dcdlsd/Atari-NetworkBox/images/prototype/networkbox-on-atari-st-front.jpg

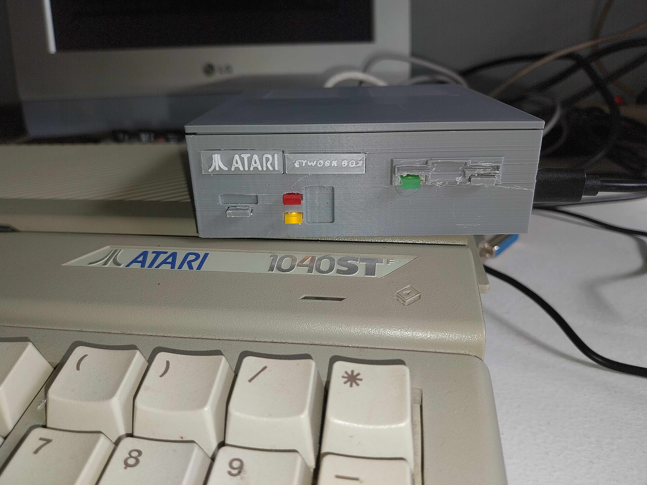
images/prototype/networkbox-on-atari-st-front.jpg
